frohro/SDR-TRX/Hardware/Simulations/ClassE Problems.asc

C1: cap; 150p
C2: cap; 550p
C3: cap; 220p
C4: cap; 430p
C5: cap; 150p
L1: ind; 200µ
L2: ind; 0.48µH
L3: ind; 0.19µH
R1: res; 50
U1: irlml2060pbf
U2: SN74ACT04
U3: SN74ACT04
U4: SN74ACT04
V1: voltage; PULSE(0 4.8 0 1n 1n 35.715n 71.428n); AC 1; Rser=100
V2: voltage; 4.5
V3: voltage; 4.5
Named nets: 0, 5V, Osc, Gate, Ant
.tran 0 11u 10u
https://community.infineon.com/t5/MOSFET-Si-SiC/Model-of-irfp260n-does-not-work-on-LTSpice/td-p/448965
