frohro/SDR-TRX/Hardware/Simulations/Bias_RE_Feedback_Testing.asc

Q1: npn; 2N5089
R1: res; {RE}
RTH: res; 100K
V1: voltage; 3
V2: voltage; 12
Named nets: 0
;op
.dc V1 1 10 3
.step param RE 1K 10K 1K
