frohro/SDR-TRX/Hardware/Simulations/Class E filter RX Effect.asc

C1: cap; 150p
C2: cap; 520p
C3: cap; 150p
C4: cap; 440p
C5: cap; 150p
C6: cap; 100n
L1: ind; 480n
L2: ind; 190n
L3: ind; 200µ
R1: res; 1Meg
V1: voltage; ""; AC 1 0; Rser=50
Named nets: 0, V_RX
.ac dec 500 1MEG 100MEG
