frohro/SDR-TRX/Hardware/Simulations/ClassE 100pf.asc

C1: cap; 100p
C2: cap; 400p
C3: cap; 400p
C4: cap; 400p
C5: cap; 100p
L1: ind; 200µ
L2: ind; .49µ
L3: ind; .18µ
R1: res; 50
R2: res; 0.2
R3: res; .3
R4: res; 0.3
U2: irlml2060pbf
V1: voltage; PULSE(0 4.8 0 1n 1n 35.715n 71.428n); AC 1; Rser=100
V2: voltage; 4.5
V3: voltage; SINE(2.5 2.5 14.1Meg); Rser=50
Named nets: 0, Gate, Ant
.tran 0 151u 150u
https://community.infineon.com/t5/MOSFET-Si-SiC/Model-of-irfp260n-does-not-work-on-LTSpice/td-p/448965
