frohro/SDR-TRX/Hardware/Simulations/diff-amp-not-qmx.asc

C1: cap; 4.7n
C2: cap; 4.7n
C3: cap; 10n
C4: cap; .1µ
R1: res; 100
R2: res; 47
R3: res; 470
R4: res; 470
R5: res; 47
R6: res; 10k
R7: res; 10k
U1: LT6231
U2: LT6231
V1: voltage; 5
V3: voltage; SINE(0 1m 1000); AC 1 0
V4: voltage; SINE(0 -1m 1000); AC 1 180
Named nets: VDDA, 0, VGND, Vop, Vom
;tran 2m
.ac dec 100 1 100MEG
;.noise V(Vop) V3 dec 100 1 100MEG
