frohro/SDR-TRX/Hardware/Simulations/Inverter.asc

U1: SN74ACT04
V1: voltage; 5
V2: voltage; SINE(2.5 1 1000); Rser=0
Named nets: 0, Osc, 5V, Vo
.tran 5m
Something is wrong with this.  It draws too much current in the A.
