frohro/SDR-TRX/Hardware/Simulations/Smoother Circuitasc.asc

C1: cap; 10µF
C2: cap; 1µF
Q1: npn; 2N2222
R1: res; 1k
R2: res; 10k
V1: voltage; SINE(5 .1 10000); AC 1 0
Named nets: 0, V_O, VB
;op
;tran 2mS
.ac dec 100 10 100k
