frohro/SDR-TRX/Hardware/Simulations/TayloeDetectorAmplifier.asc

C1: cap; {C_Sample}
C2: cap; 40pF
C3: cap; {C_Sample}
C4: cap; 40pF
C7: cap; {C_Sample}
C13: cap; {C_Sample}
R1: res; 41k
R2: res; 10
R3: res; 10
R4: res; 41k
R5: res; 1
R6: res; 10
R7: res; 1
R8: res; 10
R24: res; 0.1
R25: res; 0.1
S2: sw; MYSW
S4: sw; MYSW
S6: sw; MYSW
S7: sw; MYSW
U1: UniversalOpAmp
U2: UniversalOpAmp
V1: voltage; PULSE(0 1 0 0.001p 0.001p {SW_time} {4*SW_time})
V2: voltage; PULSE(0 1 {SW_time} 0.001p 0.001p {SW_time} {4*SW_time})
V3: voltage; SINE(0 1u {RF_Freq}); AC 1; Rser=50
V4: voltage; 5
V5: voltage; 5
V6: voltage; PULSE(0 1 {2*SW_time} 0.001p 0.001p {SW_time} {4*SW_time})
V7: voltage; PULSE(0 1 {3*SW_time} 0.001p 0.001p {SW_time} {4*SW_time})
Named nets: 0, +5V, -5V, V_0_deg, V_90_deg, V_180_deg, V_270_deg, 00, 11, 01, 10, V_I, V_Q
.model MYSW SW(Vt=0.9 Vh=0 Ron=1 Roff=100G)
.tran 0 .7m .2m
;.ac dec 10 10 1000Meg;
;.noise V(V_outQ) V3 dec 10 10 100meg
;.op
.param RF_freq=15Meg LO_freq={RF_freq - Audio_freq} LO_period={1/LO_freq} SW_time={LO_period/4}
.param C_Sample=.0155u
Signals for voltage-controlled switches 
used to simulate our multiplexer.
Power Connections
RF signal in
Multiplexer
Simulation Control
;step dec param Audio_freq 1000 10000000 1
.param Audio_freq=10000
R2 and R3 to emulate PE1NNZ
Output from inverting alone with R2=0 is: .0.9mV
Output from non-inverting input with R2=200 connected to gnd is: 0.9mV
The 200 is compensating for there being a signal connected 1/4 of the time,
The output with both connected is; 1.8mV, so both contribute equally.
The output equation is v_o = (1+(41k/50)/4)v+ - ((41k/50)/4)v-  and v- = -v+=5uV
This comes out to 2.05mV.  This shows our ideal op amp theory isn't quite dead on, about.
The filtering is not just due to the sampling capacitors.  It is also due to the op-amps.
This simulation has the roll off at almost 40 dB/decade without C2.  
You can also see this effect in the peaking at 100 kHz.  C2 removes the peaking,
and makes it drop faster in the first couple of decades, but then the unity gain
zero of the non-inverting amplifier takes over, so it only drops at 40 db/decade
thereafter.
Ideal op amps used as simulation time is long with the ones I am using.
