frohro/SDR-TRX/Hardware/Simulations/TayloeDetectorInstAmplifier.asc

C1: cap; {C_Sample}
C2: cap; 10p
C3: cap; {C_Sample}
C4: cap; 10p
C7: cap; {C_Sample}
C13: cap; {C_Sample}
R1: res; 82k
R2: res; 82k
R3: res; 200
R4: res; 4k
R5: res; 1
R6: res; 4k
R7: res; 1
R8: res; 3.9k
R9: res; 3.9k
R24: res; 1
R25: res; 1
S2: sw; MYSW
S4: sw; MYSW
S6: sw; MYSW
S7: sw; MYSW
U1: UniversalOpAmp
U2: UniversalOpAmp
U3: UniversalOpAmp
V1: voltage; PULSE(0 1 0 0.001p 0.001p {SW_time} {4*SW_time})
V2: voltage; PULSE(0 1 {SW_time} 0.001p 0.001p {SW_time} {4*SW_time})
V3: voltage; SINE(0 5u {RF_Freq}); AC 1; Rser=50
V4: voltage; 5
V5: voltage; 5
V6: voltage; PULSE(0 1 {2*SW_time} 0.001p 0.001p {SW_time} {4*SW_time})
V7: voltage; PULSE(0 1 {3*SW_time} 0.001p 0.001p {SW_time} {4*SW_time})
V8: voltage; SINE(0 5u {RF_Freq} 0 0 180); AC 1; Rser=50
Named nets: 0, +5V, -5V, V_0_deg, V_90_deg, V_180_deg, V_270_deg, 00, 11, V_filtered, 01, 10, V_filtered90, V_o
.model MYSW SW(Vt=0.9 Vh=0 Ron=1 Roff=100G)
.tran 0 0.5m 100u 1m
;.ac dec 10 10 1000Meg;
;.noise V(V_outQ) V3 dec 10 10 100meg
;.op
.param RF_freq=15Meg LO_freq={RF_freq - Audio_freq} LO_period={1/LO_freq} SW_time={LO_period/4}
.param C_Sample=10nf
Signals for voltage-controlled switches 
used to simulate our multiplexer.
Power Connections
Unfiltered RF signal
used for debugging.
Multiplexer
Simulation Control
;step dec param Audio_freq 1000 10000000 1
.param Audio_freq 10000000
This circuit has more than 40dB/decade drop off, and no peaking, because
the two poles are uncoupled, giving an overdamped response.  The two poles
are due to the sampling capacitor and C2.
