frohro/SDR-TRX/Hardware/Simulations/TayloeDetectorNonInvertingOnly.asc

C1: cap; {C_Sample}
C3: cap; {C_Sample}
C7: cap; {C_Sample}
C13: cap; {C_Sample}
R1: res; 41k
R2: res; 50
R5: res; 1
R7: res; 1
R24: res; 0.1
R25: res; 0.1
S2: sw; MYSW
S4: sw; MYSW
S6: sw; MYSW
S7: sw; MYSW
U1: UniversalOpamp2; Avol=1Meg GBW=100Meg Slew=100Meg
V1: voltage; PULSE(0 1 0 0.001p 0.001p {SW_time} {4*SW_time})
V2: voltage; PULSE(0 1 {SW_time} 0.001p 0.001p {SW_time} {4*SW_time})
V3: voltage; SINE(0 5u {RF_Freq}); AC 1; Rser=50
V4: voltage; 5
V5: voltage; 5
V6: voltage; PULSE(0 1 {2*SW_time} 0.001p 0.001p {SW_time} {4*SW_time})
V7: voltage; PULSE(0 1 {3*SW_time} 0.001p 0.001p {SW_time} {4*SW_time})
Named nets: 0, +5V, -5V, V_0_deg, V_90_deg, V_180_deg, V_270_deg, 00, 11, 01, 10
.model MYSW SW(Vt=0.9 Vh=0 Ron=1 Roff=100G)
.tran 0 0.25m 40u 5m
;.ac dec 10 10 1000Meg;
;.noise V(V_outQ) V3 dec 10 10 100meg
;.op
.param RF_freq=10Meg LO_freq={RF_freq - Audio_freq} LO_period={1/LO_freq} SW_time={LO_period/4}
.param C_Sample=16000p
Signals for voltage-controlled switches 
used to simulate our multiplexer.
Power Connections
RF signal in
Multiplexer
Simulation Control
;step oct param Audio_freq 1000 10000 1
.param Audio_freq 10000
