frohro/SDR-TRX/Hardware/Simulations/TayloeDetectorSoftrockAmplifier.asc

C1: cap; {C_Sample}
C2: cap; 220p
C3: cap; {C_Sample}
C4: cap; 220p
L1: ind2; 0.044µ
L2: ind2; 0.044
L3: ind2; 0.18
R1: res; 5k
R2: res; 10
R3: res; 10
R4: res; 10
R5: res; 5k
R6: res; 10
S1: sw; MYSW
S2: sw; MYSW
S3: sw; MYSW
S4: sw; MYSW
S5: sw; MYSW
S6: sw; MYSW
S7: sw; MYSW
S8: sw; MYSW
U1: UniversalOpamp2; Avol=1Meg GBW=100Meg Slew=100Meg
U2: UniversalOpamp2; Avol=1Meg GBW=100Meg Slew=100Meg
V1: voltage; PULSE(0 1 0 0.001p 0.001p {SW_time} {4*SW_time})
V2: voltage; PULSE(0 1 {SW_time} 0.001p 0.001p {SW_time} {4*SW_time})
V3: voltage; SINE(0 5u {RF_Freq}); AC 1; Rser=50
V4: voltage; 5
V5: voltage; 5
V6: voltage; PULSE(0 1 {2*SW_time} 0.001p 0.001p {SW_time} {4*SW_time})
V7: voltage; PULSE(0 1 {3*SW_time} 0.001p 0.001p {SW_time} {4*SW_time})
Named nets: 0, +5V, -5V, V_0_deg, V_90_deg, V_180_deg, V_270_deg, P, M, 1A, 2A, I, Q
.model MYSW SW(Vt=0.9 Vh=0 Ron=1 Roff=100G)
.tran 0 0.25m 40u 5m
;.ac dec 10 10 1000Meg;
;.noise V(V_outQ) V3 dec 10 10 100meg
;.op
.param RF_freq=14.2Meg LO_freq={RF_freq - Audio_freq} LO_period={1/LO_freq} SW_time={LO_period/4}
.param C_Sample=0.047u
Signals for voltage-controlled switches 
used to simulate our multiplexer.
Power Connections
RF signal in
Multiplexer
Simulation Control
;step oct param Audio_freq 1000 10000 1
.param Audio_freq 10000
1B1
1B2
1B3
1B4
2B1
2B2
2B3
2B4
K1 L1 L2 L3 1
8 turns primary, 4 turns bifilar secondary
Design notes:  Due to the C_samlple:  BW = 1/(4 pi RC_sample)
where R = ((50/4)+10)||10
Gain = -5k/(10+10 + 50/4)
Noise Figure: 9.4 dB
NF calculated from: http://dicks-website.eu/noisecalculator/index.html
