frohro/SDR-TRX/Hardware/Simulations/Test_Inverter.asc

U1: SN74ACT04
V1: voltage; 5
V2: voltage; PULSE(0 5 0 0 0 1u 2u)
Named nets: 0, In, Out, VDD
.tran 5u
